celeritous/STM32F745VE_Module/STM32F745VE_Firmware/STM32F745VE/Src/sd_diskio.c

/**
  ******************************************************************************
  * @file    sd_diskio.c (based on sd_diskio_dma_template.c v2.0.2)
  * @brief   SD Disk I/O driver
  ******************************************************************************
  * This notice applies to any and all portions of this file
  * that are not between comment pairs USER CODE BEGIN and
  * USER CODE END. Other portions of this file, whether 
  * inserted by the user or by software development tools
  * are owned by their respective copyright owners.
  *
  * Copyright (c) 2018 STMicroelectronics International N.V. 
  * All rights reserved.
  *
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
  ******************************************************************************
  */ 
/* USER CODE BEGIN firstSection */
/* can be used to modify / undefine following code or add new definitions */
/* USER CODE END firstSection*/

/* Includes ------------------------------------------------------------------*/
#include "ff_gen_drv.h"
#include "sd_diskio.h"


 /*
 * the following Timeout is useful to give the control back to the applications
 * in case of errors in either BSP_SD_ReadCpltCallback() or BSP_SD_WriteCpltCallback()
 * the value by default is as defined in the BSP platform driver otherwise 30 secs
 */
#define SD_TIMEOUT 30 * 1000

#define SD_DEFAULT_BLOCK_SIZE 512

/*
 * Depending on the use case, the SD card initialization could be done at the
 * application level: if it is the case define the flag below to disable
 * the BSP_SD_Init() call in the SD_Initialize() and add a call to 
 * BSP_SD_Init() elsewhere in the application.
 */
/* USER CODE BEGIN disableSDInit */
/* #define DISABLE_SD_INIT */
/* USER CODE END disableSDInit */

/* 
 * when using cachable memory region, it may be needed to maintain the cache
 * validity. Enable the define below to activate a cache maintenance at each
 * read and write operation.
 * Notice: This is applicable only for cortex M7 based platform.
 */
/* USER CODE BEGIN enableSDDmaCacheMaintenance */
/* #define ENABLE_SD_DMA_CACHE_MAINTENANCE  1 */
/* USER CODE BEGIN enableSDDmaCacheMaintenance */

/* Disk status */
static volatile DSTATUS Stat = STA_NOINIT;

static volatile  UINT  WriteStatus = 0, ReadStatus = 0;
static DSTATUS SD_CheckStatus(BYTE lun);
DSTATUS SD_initialize (BYTE);
DSTATUS SD_status (BYTE);
DRESULT SD_read (BYTE, BYTE*, DWORD, UINT);
#if _USE_WRITE == 1
  DRESULT SD_write (BYTE, const BYTE*, DWORD, UINT);
#endif /* _USE_WRITE == 1 */
#if _USE_IOCTL == 1
  DRESULT SD_ioctl (BYTE, BYTE, void*);
#endif  /* _USE_IOCTL == 1 */

const Diskio_drvTypeDef  SD_Driver =
{
  SD_initialize,
  SD_status,
  SD_read,
#if  _USE_WRITE == 1
  SD_write,
#endif /* _USE_WRITE == 1 */

#if  _USE_IOCTL == 1
  SD_ioctl,
#endif /* _USE_IOCTL == 1 */
};

/* USER CODE BEGIN beforeFunctionSection */
/* can be used to modify / undefine following code or add new code */
/* USER CODE END beforeFunctionSection */

static DSTATUS SD_CheckStatus(BYTE lun)
{
  Stat = STA_NOINIT;

  if(BSP_SD_GetCardState() == MSD_OK)
  {
    Stat &= ~STA_NOINIT;
  }

  return Stat;
}

/**
  * @brief  Initializes a Drive
  * @param  lun : not used
  * @retval DSTATUS: Operation status
  */
DSTATUS SD_initialize(BYTE lun)
{
  Stat = STA_NOINIT;
#if !defined(DISABLE_SD_INIT)

  if(BSP_SD_Init() == MSD_OK)
  {
    Stat = SD_CheckStatus(lun);
  }

#else
  Stat = SD_CheckStatus(lun);
#endif
  return Stat;
}

/**
  * @brief  Gets Disk Status
  * @param  lun : not used
  * @retval DSTATUS: Operation status
  */
DSTATUS SD_status(BYTE lun)
{
  return SD_CheckStatus(lun);
}

/* USER CODE BEGIN beforeReadSection */
/* can be used to modify previous code / undefine following code / add new code */
/* USER CODE END beforeReadSection */
/**
  * @brief  Reads Sector(s)
  * @param  lun : not used
  * @param  *buff: Data buffer to store read data
  * @param  sector: Sector address (LBA)
  * @param  count: Number of sectors to read (1..128)
  * @retval DRESULT: Operation result
  */
DRESULT SD_read(BYTE lun, BYTE *buff, DWORD sector, UINT count)
{
  DRESULT res = RES_ERROR;
  ReadStatus = 0;
  uint32_t timeout;
#if (ENABLE_SD_DMA_CACHE_MAINTENANCE == 1)
  uint32_t alignedAddr;
#endif

  if(BSP_SD_ReadBlocks_DMA((uint32_t*)buff,
                           (uint32_t) (sector),
                           count) == MSD_OK)
  {
    /* Wait that the reading process is completed or a timeout occurs */
    timeout = HAL_GetTick();
    while((ReadStatus == 0) && ((HAL_GetTick() - timeout) < SD_TIMEOUT))
    {
    }
    /* incase of a timeout return error */
    if (ReadStatus == 0)
    {
      res = RES_ERROR;
    }
    else
    {
      ReadStatus = 0;
      timeout = HAL_GetTick();

      while((HAL_GetTick() - timeout) < SD_TIMEOUT)
      {
        if (BSP_SD_GetCardState() == SD_TRANSFER_OK)
        {
          res = RES_OK;
#if (ENABLE_SD_DMA_CACHE_MAINTENANCE == 1)
            /*
               the SCB_InvalidateDCache_by_Addr() requires a 32-Byte aligned address,
               adjust the address and the D-Cache size to invalidate accordingly.
             */
            alignedAddr = (uint32_t)buff & ~0x1F;
            SCB_InvalidateDCache_by_Addr((uint32_t*)alignedAddr, count*BLOCKSIZE + ((uint32_t)buff - alignedAddr));
#endif
           break;
        }
      }
    }
  }

  return res;
}

/* USER CODE BEGIN beforeWriteSection */
/* can be used to modify previous code / undefine following code / add new code */
/* USER CODE END beforeWriteSection */
/**
  * @brief  Writes Sector(s)
  * @param  lun : not used
  * @param  *buff: Data to be written
  * @param  sector: Sector address (LBA)
  * @param  count: Number of sectors to write (1..128)
  * @retval DRESULT: Operation result
  */
#if _USE_WRITE == 1
DRESULT SD_write(BYTE lun, const BYTE *buff, DWORD sector, UINT count)
{
  DRESULT res = RES_ERROR;
  WriteStatus = 0;
  uint32_t timeout;
#if (ENABLE_SD_DMA_CACHE_MAINTENANCE == 1)
  uint32_t alignedAddr;
  /*
   the SCB_CleanDCache_by_Addr() requires a 32-Byte aligned address
   adjust the address and the D-Cache size to clean accordingly.
   */
  alignedAddr = (uint32_t)buff &  ~0x1F;
  SCB_CleanDCache_by_Addr((uint32_t*)alignedAddr, count*BLOCKSIZE + ((uint32_t)buff - alignedAddr));
#endif

  if(BSP_SD_WriteBlocks_DMA((uint32_t*)buff,
                            (uint32_t) (sector),
                            count) == MSD_OK)
  {
    /* Wait that writing process is completed or a timeout occurs */

    timeout = HAL_GetTick();
    while((WriteStatus == 0) && ((HAL_GetTick() - timeout) < SD_TIMEOUT))
    {
    }
    /* incase of a timeout return error */
    if (WriteStatus == 0)
    {
      res = RES_ERROR;
    }
    else
    {
      WriteStatus = 0;
      timeout = HAL_GetTick();

      while((HAL_GetTick() - timeout) < SD_TIMEOUT)
      {
        if (BSP_SD_GetCardState() == SD_TRANSFER_OK)
        {
          res = RES_OK;
          break;
        }
      }
    }
  }

  return res;
}
#endif /* _USE_WRITE == 1 */

/* USER CODE BEGIN beforeIoctlSection */
/* can be used to modify previous code / undefine following code / add new code */
/* USER CODE END beforeIoctlSection */
/**
  * @brief  I/O control operation
  * @param  lun : not used
  * @param  cmd: Control code
  * @param  *buff: Buffer to send/receive control data
  * @retval DRESULT: Operation result
  */
#if _USE_IOCTL == 1
DRESULT SD_ioctl(BYTE lun, BYTE cmd, void *buff)
{
  DRESULT res = RES_ERROR;
  BSP_SD_CardInfo CardInfo;

  if (Stat & STA_NOINIT) return RES_NOTRDY;

  switch (cmd)
  {
  /* Make sure that no pending write process */
  case CTRL_SYNC :
    res = RES_OK;
    break;

  /* Get number of sectors on the disk (DWORD) */
  case GET_SECTOR_COUNT :
    BSP_SD_GetCardInfo(&CardInfo);
    *(DWORD*)buff = CardInfo.LogBlockNbr;
    res = RES_OK;
    break;

  /* Get R/W sector size (WORD) */
  case GET_SECTOR_SIZE :
    BSP_SD_GetCardInfo(&CardInfo);
    *(WORD*)buff = CardInfo.LogBlockSize;
    res = RES_OK;
    break;

  /* Get erase block size in unit of sector (DWORD) */
  case GET_BLOCK_SIZE :
    BSP_SD_GetCardInfo(&CardInfo);
    *(DWORD*)buff = CardInfo.LogBlockSize / SD_DEFAULT_BLOCK_SIZE;
    res = RES_OK;
    break;

  default:
    res = RES_PARERR;
  }

  return res;
}
#endif /* _USE_IOCTL == 1 */

/* USER CODE BEGIN afterIoctlSection */
/* can be used to modify previous code / undefine following code / add new code */
/* USER CODE END afterIoctlSection */

/* USER CODE BEGIN callbackSection */ 
/* can be used to modify / following code or add new code */
/* USER CODE END callbackSection */
/**
  * @brief Tx Transfer completed callbacks
  * @param hsd: SD handle
  * @retval None
  */

 /*
   ===============================================================================
    Select the correct function signature depending on your platform.
    please refer to the file "stm32xxxx_eval_sd.h" to verify the correct function
    prototype
   ===============================================================================
  */
//void BSP_SD_WriteCpltCallback(uint32_t SdCard)
void BSP_SD_WriteCpltCallback(void)
{
  WriteStatus = 1;
}

/**
  * @brief Rx Transfer completed callbacks
  * @param hsd: SD handle
  * @retval None
  */

  /*
   ===============================================================================
    Select the correct function signature depending on your platform.
    please refer to the file "stm32xxxx_eval_sd.h" to verify the correct function
    prototype
   ===============================================================================
  */
//void BSP_SD_ReadCpltCallback(uint32_t SdCard)
void BSP_SD_ReadCpltCallback(void)
{
  ReadStatus = 1;
}

/* USER CODE BEGIN lastSection */ 
/* can be used to modify / undefine previous code or add new code */
/* USER CODE END lastSection */

/************************ (C) COPYRIGHT STMicroelectronics *****END OF FILE****/
